tuxedocurly/mantaray_keyboard/img/Diode Placement.png

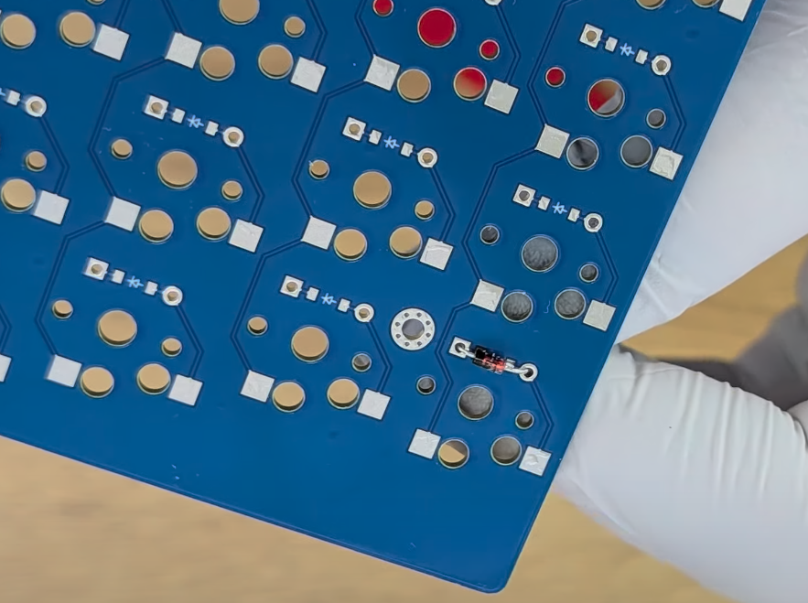
img/Diode Placement.png
