tuxedocurly/mantaray_keyboard/img/hotswap_sockets.png

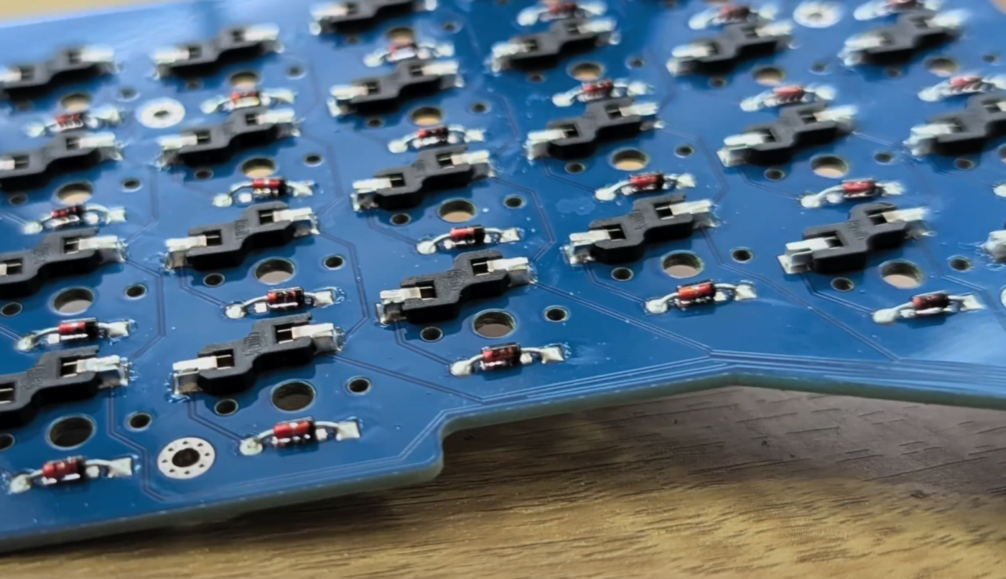
img/hotswap_sockets.png
