tuxedocurly/mantaray_keyboard/img/PXL_20250109_180317979.jpg

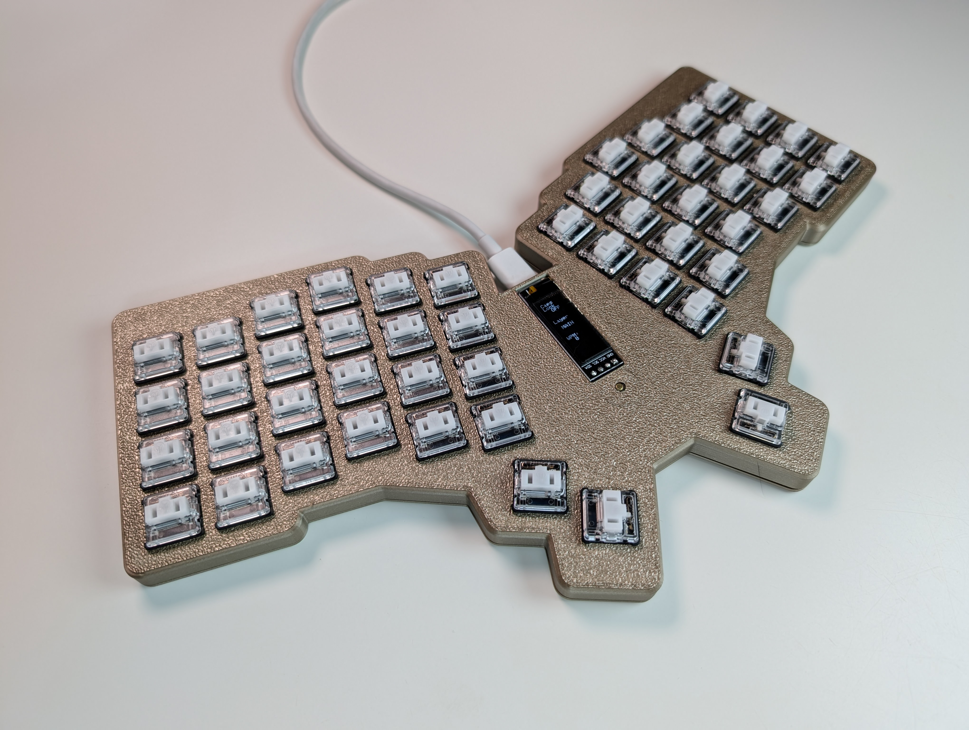
img/PXL_20250109_180317979.jpg
