tuxedocurly/mantaray_keyboard/img/PXL_20250109_202824409.jpg

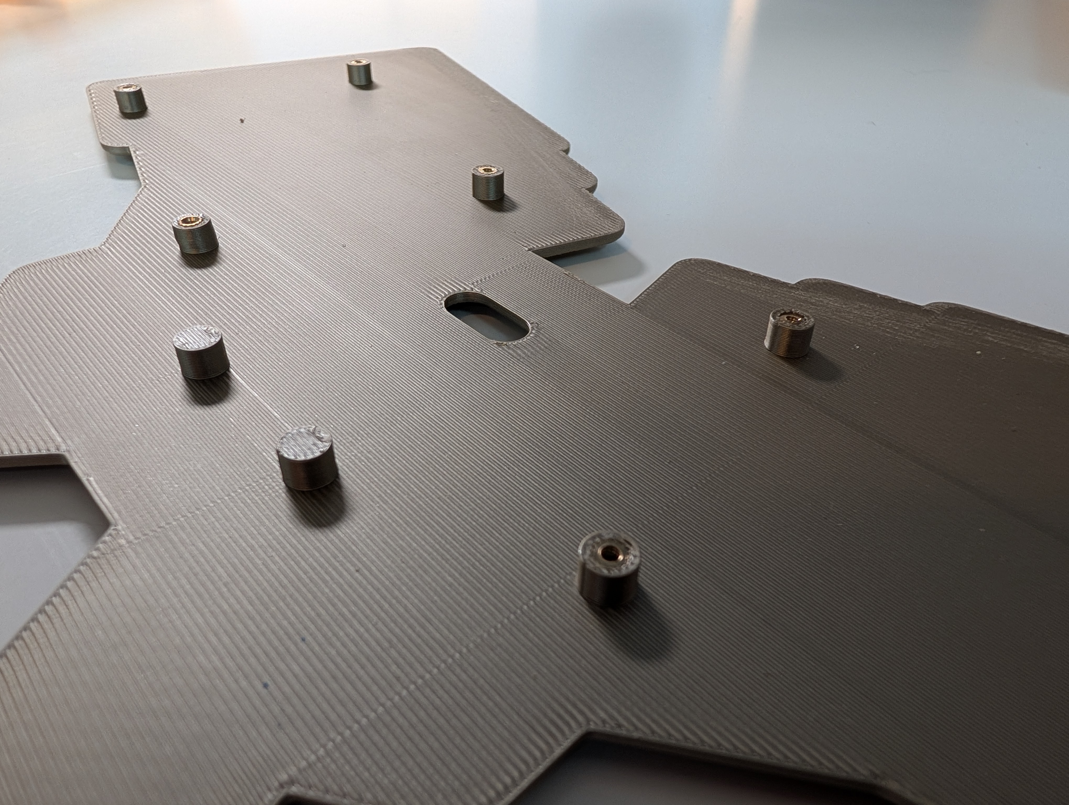
img/PXL_20250109_202824409.jpg
