tuxedocurly/mantaray_keyboard/img/PXL_20250109_202859032.jpg

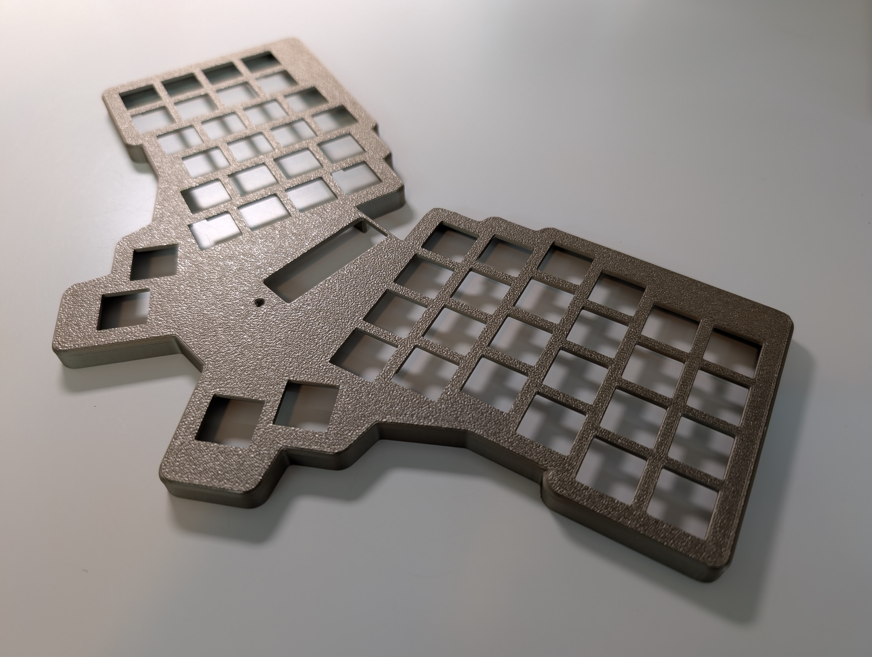
img/PXL_20250109_202859032.jpg
