tuxedocurly/mantaray_keyboard/img/PXL_20250112_193250812.jpg

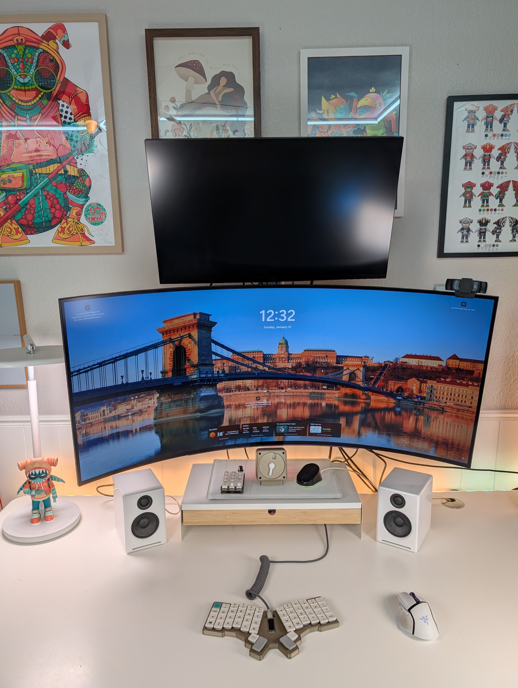
img/PXL_20250112_193250812.jpg
