tuxedocurly/mantaray_keyboard/img/reset_button.png

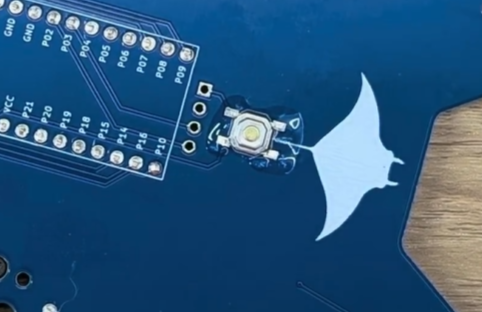
img/reset_button.png
