tuxedocurly/mantaray_keyboard/mantaray-pcb/mantaray.kicad_pcb

## KiCad design mantaray-pcb/mantaray.kicad_pcb (2025-01-02)

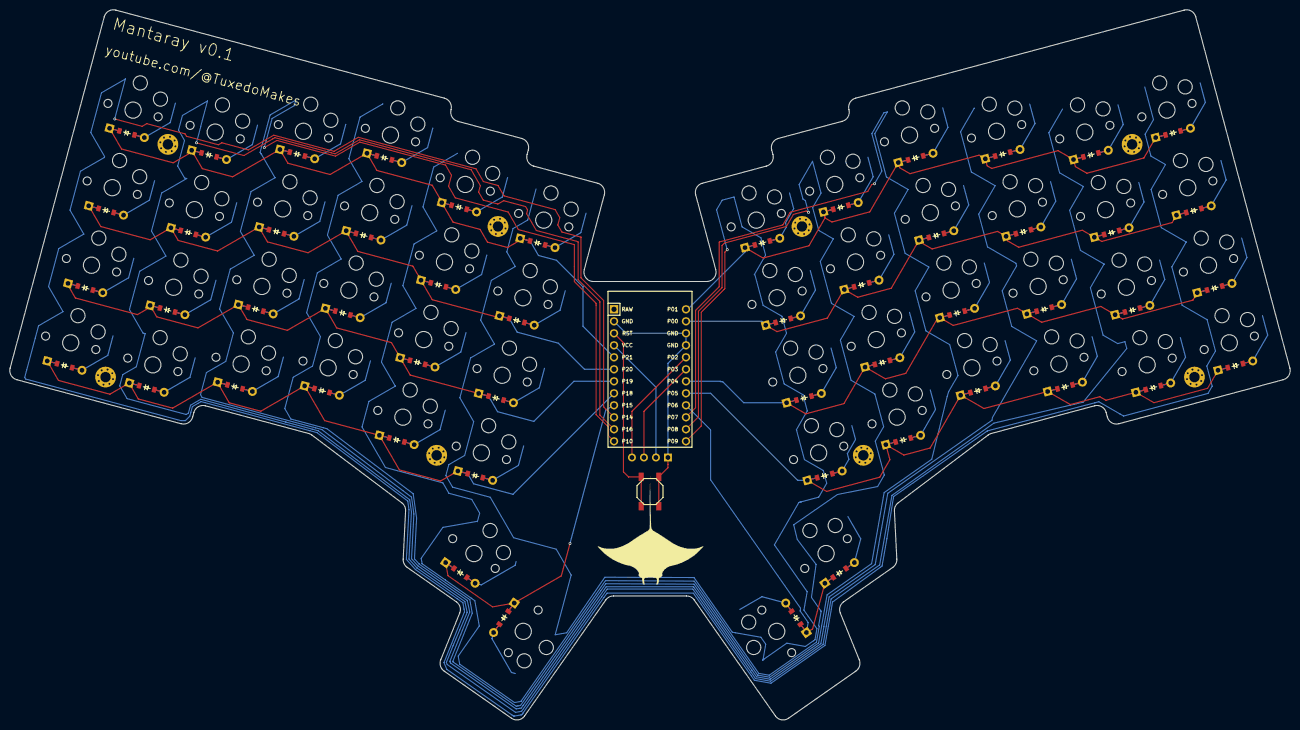
[picture p17: board mantaray.kicad_pcb from above]

Board: 2 copper layers, 271.1 x 150.3 mm, 115 parts (0 on the bottom side), 73 nets.

Parts:
B1: SW_TACT_ALPS_SKQGABE010
D1, D2, D3, D4, D5, D6, D7, D8, D9, D10, D11, D12, D13, D14, D15, D16, D17, D18, D19, D20, D21, D22, D23, D24, D25, D26, D27, D28, D29, D30, D31, D32, D33, D34, D35, D36, D37, D38, D39, D40, D41, D42, D43, D44, D45, D46, D47, D48, D49, D50, D51, D52: ComboDiode
MCU1: ProMicro
OLED1: OLED; OLED_headers
S1, S2, S3, S4, S5, S6, S7, S8, S9, S10, S11, S12, S13, S14, S15, S16, S17, S18, S19, S20, S21, S22, S23, S24, S25, S26, S27, S28, S29, S30, S31, S32, S33, S34, S35, S36, S37, S38, S39, S40, S41, S42, S43, S44, S45, S46, S47, S48, S49, S50, S51, S52: PG1350
_1, _2, _3, _4, _5, _6, _7, _8: MountingHole_2.2mm_M2_Pad_Via

Connections:
GND: B1.1, MCU1.2, MCU1.15, MCU1.16, OLED1.1
P0: D29.1, D33.1, D37.1, D41.1, D45.1, D49.1, MCU1.14
P1: D30.1, D34.1, D38.1, D42.1, D46.1, D50.1, MCU1.13
P2: MCU1.17, OLED1.4
P3: MCU1.18, OLED1.3
P4: D28.1, D32.1, D36.1, D40.1, D44.1, D48.1, MCU1.19
P5: D27.1, D31.1, D35.1, D39.1, D43.1, D47.1, MCU1.20
P6: D51.1, D52.1, MCU1.21
P7: MCU1.22, S13.1, S14.1, S15.1, S16.1, S39.1, S40.1, S41.1, S42.1
P8: MCU1.23, S17.1, S18.1, S19.1, S20.1, S25.1, S43.1, S44.1, S45.1, S46.1, S51.1
P9: MCU1.24, S21.1, S22.1, S23.1, S24.1, S26.1, S47.1, S48.1, S49.1, S50.1, S52.1
P10: MCU1.12, S9.1, S10.1, S11.1, S12.1, S35.1, S36.1, S37.1, S38.1
P14: MCU1.10, S1.1, S2.1, S3.1, S4.1, S27.1, S28.1, S29.1, S30.1
P15: D25.1, D26.1, MCU1.9
P16: MCU1.11, S5.1, S6.1, S7.1, S8.1, S31.1, S32.1, S33.1, S34.1
P18: D1.1, D5.1, D9.1, D13.1, D17.1, D21.1, MCU1.8
P19: D2.1, D6.1, D10.1, D14.1, D18.1, D22.1, MCU1.7
P20: D3.1, D7.1, D11.1, D15.1, D19.1, D23.1, MCU1.6
P21: D4.1, D8.1, D12.1, D16.1, D20.1, D24.1, MCU1.5
RST: B1.2, MCU1.3
VCC: MCU1.4, OLED1.2
index_bottom: D17.2, S17.2
index_home: D18.2, S18.2
index_num: D20.2, S20.2
index_top: D19.2, S19.2
inner_bottom: D21.2, S21.2
inner_home: D22.2, S22.2
inner_num: D24.2, S24.2
inner_top: D23.2, S23.2
layer_cluster: D25.2, S25.2
middle_bottom: D13.2, S13.2
middle_home: D14.2, S14.2
middle_num: D16.2, S16.2
middle_top: D15.2, S15.2
mirror_index_bottom: D43.2, S43.2
mirror_index_home: D44.2, S44.2
mirror_index_num: D46.2, S46.2
mirror_index_top: D45.2, S45.2
mirror_inner_bottom: D47.2, S47.2
mirror_inner_home: D48.2, S48.2
mirror_inner_num: D50.2, S50.2
mirror_inner_top: D49.2, S49.2
mirror_layer_cluster: D51.2, S51.2
mirror_middle_bottom: D39.2, S39.2
mirror_middle_home: D40.2, S40.2
mirror_middle_num: D42.2, S42.2
mirror_middle_top: D41.2, S41.2
mirror_outer_bottom: D27.2, S27.2
mirror_outer_home: D28.2, S28.2
mirror_outer_num: D30.2, S30.2
mirror_outer_top: D29.2, S29.2
mirror_pinky_bottom: D31.2, S31.2
mirror_pinky_home: D32.2, S32.2
mirror_pinky_num: D34.2, S34.2
mirror_pinky_top: D33.2, S33.2
mirror_ring_bottom: D35.2, S35.2
mirror_ring_home: D36.2, S36.2
mirror_ring_num: D38.2, S38.2
mirror_ring_top: D37.2, S37.2
mirror_space_cluster: D52.2, S52.2
outer_bottom: D1.2, S1.2
outer_home: D2.2, S2.2
outer_num: D4.2, S4.2
outer_top: D3.2, S3.2
pinky_bottom: D5.2, S5.2
pinky_home: D6.2, S6.2
pinky_num: D8.2, S8.2
pinky_top: D7.2, S7.2
ring_bottom: D9.2, S9.2
ring_home: D10.2, S10.2
ring_num: D12.2, S12.2
ring_top: D11.2, S11.2
space_cluster: D26.2, S26.2
